mcjurij/mfm/hardware/counter_atmega328p_v2/counter_mcu_v2.kicad_sch

## KiCad design hardware/counter_atmega328p_v2/counter_mcu_v2.kicad_sch (2023-09-27)

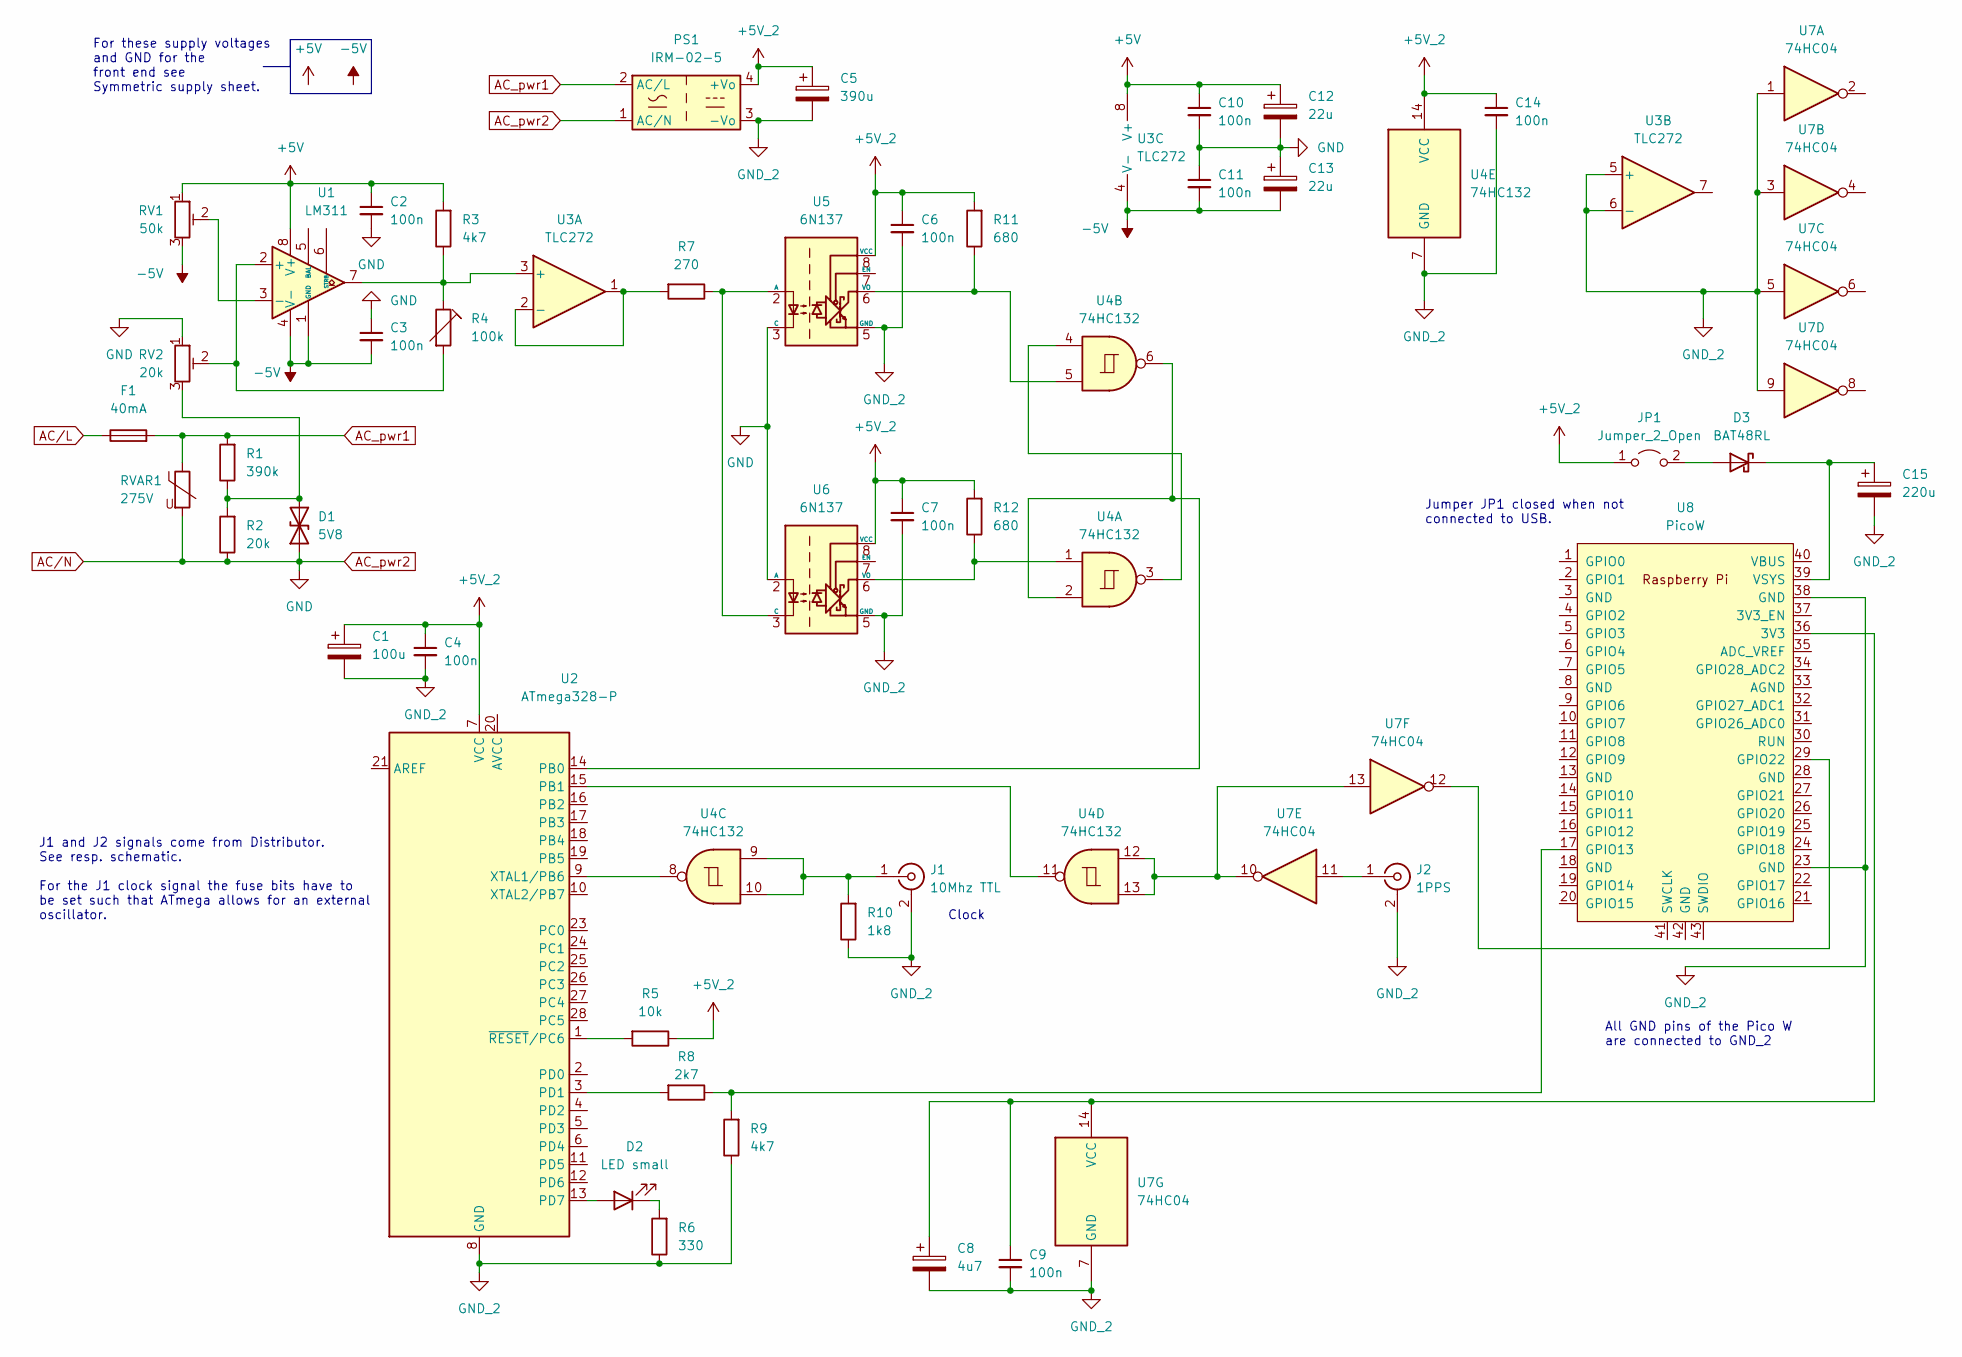
[picture p16: schematic counter_mcu_v2.kicad_sch]

Parts:
C1: 100u
C2, C3, C4, C6, C7, C9, C10, C11, C14: 100n
C5: 390u
C8: 4u7
C12, C13: 22u
C15: 220u
D1: 5V8
D2: LED small
D3: BAT48RL; D_DO-35_SOD27_P7.62mm_Horizontal
F1: 40mA
J1: 10Mhz TTL
J2: 1PPS
JP1: Jumper_2_Open
PS1: IRM-02-5; Converter_ACDC_MeanWell_IRM-02-xx_THT
R1: 390k
R2: 20k
R3, R9: 4k7
R4: 100k
R5: 10k
R6: 330
R7: 270
R8: 2k7
R10: 1k8
R11, R12: 680
RV1: 50k
RV2: 20k
RVAR1: 275V
U1: LM311
U2: ATmega328-P; DIP-28_W7.62mm
U3: TLC272
U4: 74HC132
U5, U6: 6N137; DIP-8_W7.62mm
U7: 74HC04
U8: PicoW; RPi_Pico_SMD_TH

Connections:
+5V: C2.1, C10.1, C12.1, R3.2, RV1.1, U1.8 (V+), U3.8 (V+)
+5V_2: C1.1, C4.1, C5.1, C6.1, C7.1, C14.1, JP1.1 (A), PS1.4 (+Vo), R5.1, R11.2, R12.2, U2.7 (VCC), U4.14 (VCC), U5.8 (VCC), U6.8 (VCC)
-5V: C3.2, C11.2, C13.2, RV1.3, U1.1 (GND), U1.4 (V-), U3.4 (V-)
AC_pwr1: F1.2, PS1.2 (AC/L), R1.2, RVAR1.1
AC_pwr2: C2.2, C3.1, C10.2, C11.1, C12.2, C13.1, D1.1 (A1), PS1.1 (AC/N), R2.1, RV2.1, RVAR1.2, U5.3 (C), U6.2 (A)
AC/L: F1.1
GND_2: C1.2, C4.2, C5.2, C6.2, C7.2, C8.2, C9.2, C14.2, C15.2, J1.2 (Ext), J2.2 (Ext), PS1.3 (-Vo), R6.1, R9.1, R10.1, U2.8 (GND), U2.22 (GND), U3.5 (+), U3.6 (-), U4.7 (GND), U5.5 (GND), U6.5 (GND), U7.1, U7.3, U7.5, U7.7 (GND), U7.9, U8.23 (GND), U8.38 (GND)
unnamed: C8.1, C9.1, U7.14 (VCC), U8.36 (3V3)
unnamed: C15.1, D3.1 (K), U8.39 (VSYS)
unnamed: D1.2 (A2), R1.1, R2.2, RV2.3
unnamed: D2.1 (K), R6.2
unnamed: D2.2 (A), U2.13 (PD7)
unnamed: D3.2 (A), JP1.2 (B)
unnamed: J1.1 (In), R10.2, U4.9, U4.10
unnamed: J2.1 (In), U7.11
unnamed: R3.1, R4.1, U1.7, U3.3 (+)
unnamed: R4.2, RV2.2, U1.2 (+)
unnamed: R5.2, U2.1 (~RESET/PC6)
unnamed: R7.1, U5.2 (A), U6.3 (C)
unnamed: R7.2, U3.1, U3.2 (-)
unnamed: R8.1, R9.2, U8.17 (GPIO13)
unnamed: R8.2, U2.3 (PD1)
unnamed: R11.1, U4.5, U5.6 (VO)
unnamed: R12.1, U4.1, U6.6 (VO)
unnamed: RV1.2, U1.3 (-)
unnamed: U2.9 (XTAL1/PB6), U4.8
unnamed: U2.14 (PB0), U4.2, U4.6
unnamed: U2.15 (PB1), U4.11
unnamed: U4.3, U4.4
unnamed: U4.12, U4.13, U7.10, U7.13
unnamed: U7.12, U8.29 (GPIO22)

Notes on the sheet:
J1 and J2 signals come from Distributor. See resp. schematic. For the J1 clock signal the fuse bits have to be set such that ATmega allows for an external oscillator.
Clock
Jumper JP1 closed when not connected to USB.
All GND pins of the Pico W are connected to GND_2
For these supply voltages and GND for the front end see Symmetric supply sheet.
