mcjurij/mfm/hardware/counter_ps/counter_ps.kicad_sch

## KiCad design hardware/counter_ps/counter_ps.kicad_sch (2023-12-20)

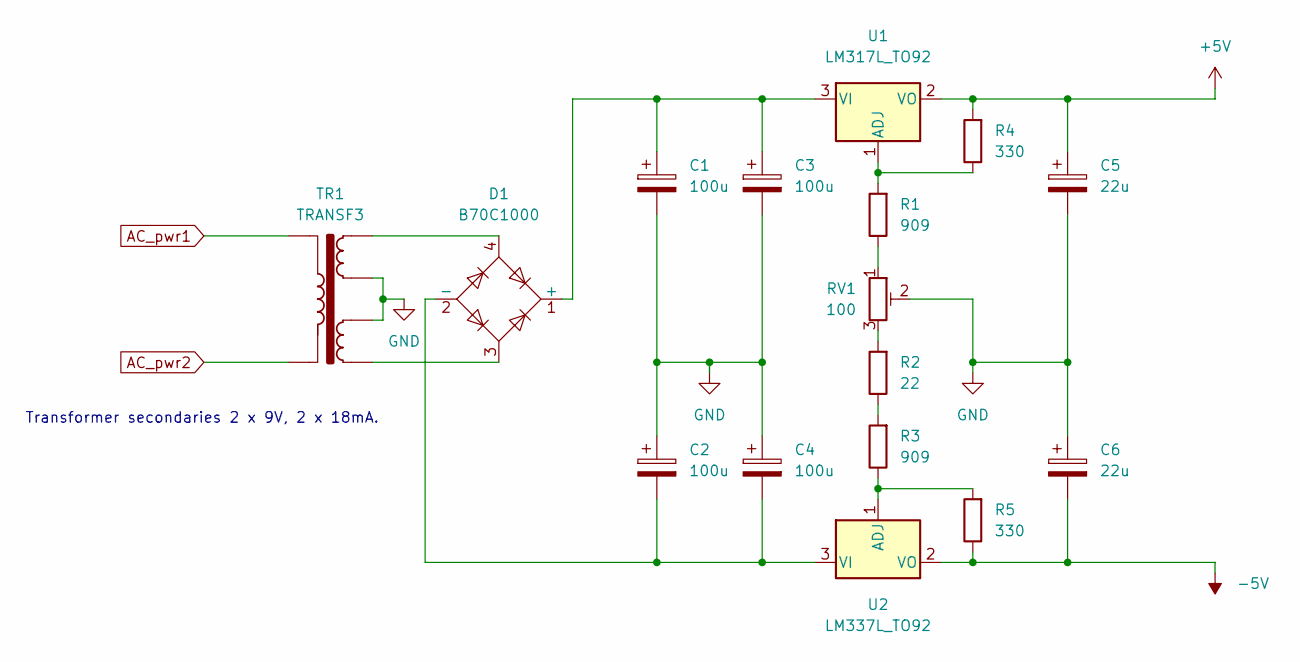
[picture p17: schematic counter_ps.kicad_sch]

Parts:
C1, C2, C3, C4: 100u
C5, C6: 22u
D1: B70C1000; Diode_Bridge_DIP-4_W7.62mm_P5.08mm
R1, R3: 909
R2: 22
R4, R5: 330
RV1: 100
TR1: TRANSF3
U1: LM317L_TO92; TO-92_Inline
U2: LM337L_TO92; TO-92_Inline

Connections:
+5V: C5.1, R4.2, U1.2 (VO)
-5V: C6.2, R5.1, U2.2 (VO)
AC_pwr1: TR1.1
AC_pwr2: TR1.2
GND: C1.2, C2.1, C3.2, C4.1, C5.2, C6.1, RV1.2, TR1.4, TR1.5
unnamed: C1.1, C3.1, D1.1 (+), U1.3 (VI)
unnamed: C2.2, C4.2, D1.2 (-), U2.3 (VI)
unnamed: D1.3, TR1.6
unnamed: D1.4, TR1.3
unnamed: R1.1, RV1.1
unnamed: R1.2, R4.1, U1.1 (ADJ)
unnamed: R2.1, R3.2
unnamed: R2.2, RV1.3
unnamed: R3.1, R5.2, U2.1 (ADJ)

Notes on the sheet:
Transformer secondaries 2 x 9V, 2 x 18mA.
