mcjurij/mfm/hardware/distributor/counter_distributor.kicad_sch

## KiCad design hardware/distributor/counter_distributor.kicad_sch (2023-09-27)

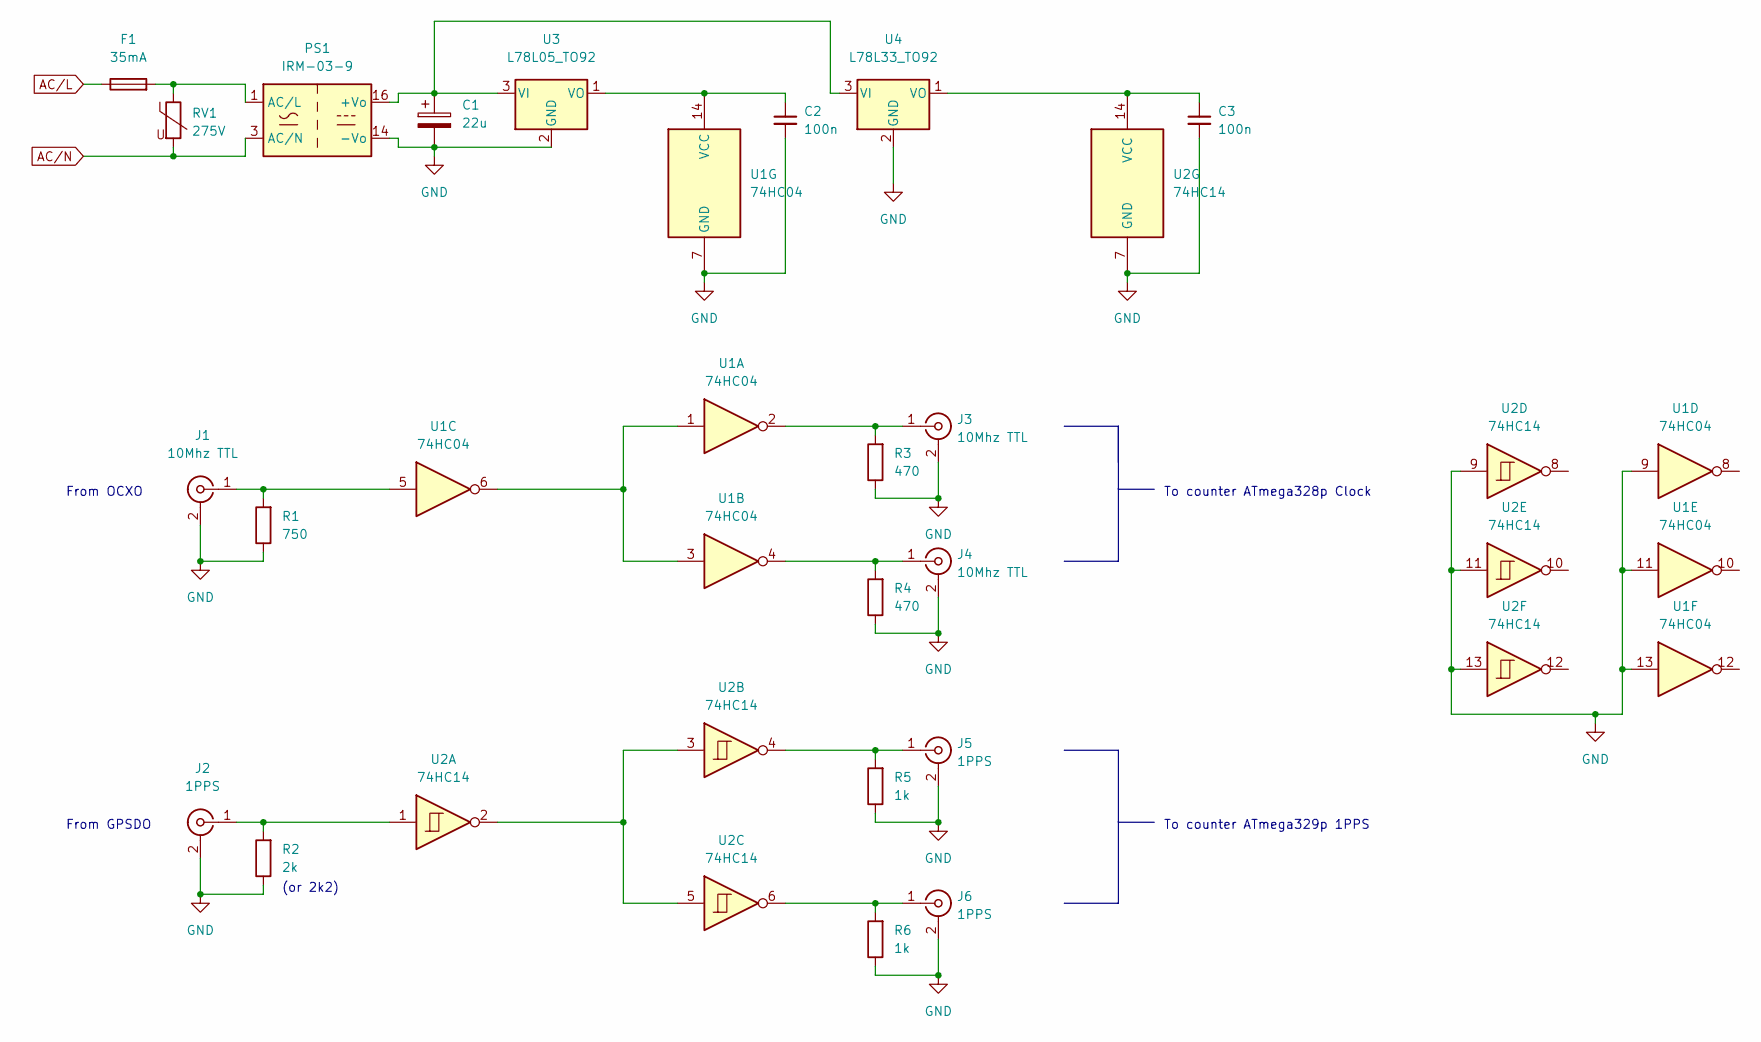
[picture p18: schematic counter_distributor.kicad_sch]

Parts:
C1: 22u
C2, C3: 100n
F1: 35mA
J1, J3, J4: 10Mhz TTL
J2, J5, J6: 1PPS
PS1: IRM-03-9; Converter_ACDC_MeanWell_IRM-03-xx_THT
R1: 750
R2: 2k
R3, R4: 470
R5, R6: 1k
RV1: 275V
U1: 74HC04
U2: 74HC14
U3: L78L05_TO92; TO-92_Inline
U4: L78L33_TO92; TO-92_Inline

Connections:
AC/L: F1.1
AC/N: PS1.3 (AC/N), RV1.2
GND: C1.2, C2.2, C3.2, J1.2 (Ext), J2.2 (Ext), J3.2 (Ext), J4.2 (Ext), J5.2 (Ext), J6.2 (Ext), PS1.14 (-Vo), R1.1, R2.1, R3.1, R4.1, R5.1, R6.1, U1.7 (GND), U1.9, U1.11, U1.13, U2.7 (GND), U2.9, U2.11, U2.13, U3.2 (GND), U4.2 (GND)
unnamed: C1.1, PS1.16 (+Vo), U3.3 (VI), U4.3 (VI)
unnamed: C2.1, U1.14 (VCC), U3.1 (VO)
unnamed: C3.1, U2.14 (VCC), U4.1 (VO)
unnamed: F1.2, PS1.1 (AC/L), RV1.1
unnamed: J1.1 (In), R1.2, U1.5
unnamed: J2.1 (In), R2.2, U2.1
unnamed: J3.1 (In), R3.2, U1.2
unnamed: J4.1 (In), R4.2, U1.4
unnamed: J5.1 (In), R5.2, U2.4
unnamed: J6.1 (In), R6.2, U2.6
unnamed: U1.1, U1.3, U1.6
unnamed: U2.2, U2.3, U2.5

Notes on the sheet:
(or 2k2)
To counter ATmega329p 1PPS
From GPSDO
From OCXO
To counter ATmega328p Clock
